BrianEnigma/PPP/Pixelart/headstone2.png

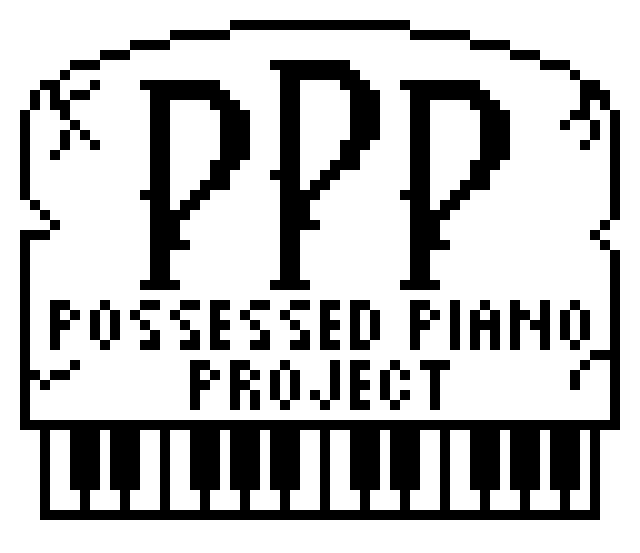
Pixelart/headstone2.png
